costa-victor/wireless-robotic-arm-arduino/3D Files/Garra adaptada/EBA_01.00.013_R01_right_finger.STL

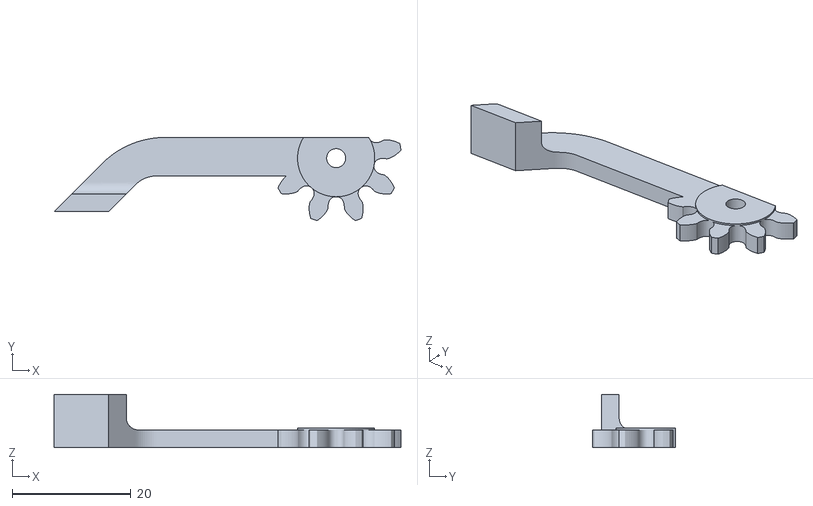
[picture p15: CAD file, 2020-02-10]
3D Files/Garra adaptada/EBA_01.00.013_R01_right_finger.STL
58.4 x 14.0 x 9.00
