costa-victor/wireless-robotic-arm-arduino/3D Files/stl/parte 9 - modificadaAutocad.stl

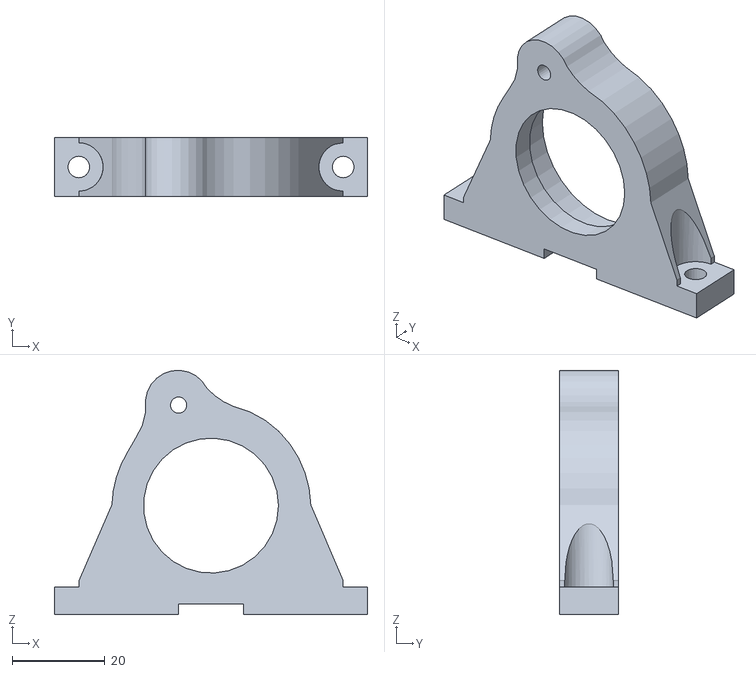
[picture p16: CAD file, 2020-02-10]
3D Files/stl/parte 9 - modificadaAutocad.stl
67.7 x 12.8 x 52.8
