costa-victor/wireless-robotic-arm-arduino/3D Files/Garra adaptada/EBA_01.00.004_forward_drive_arm.STL

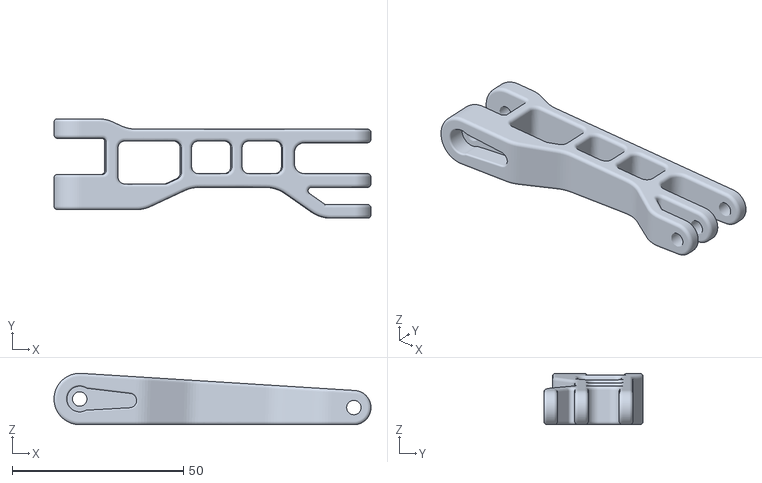
[picture p17: CAD file, 2020-02-10]
3D Files/Garra adaptada/EBA_01.00.004_forward_drive_arm.STL
92.5 x 29.0 x 15.0
