costa-victor/wireless-robotic-arm-arduino/3D Files/stl/parte 23 - autocad.stl

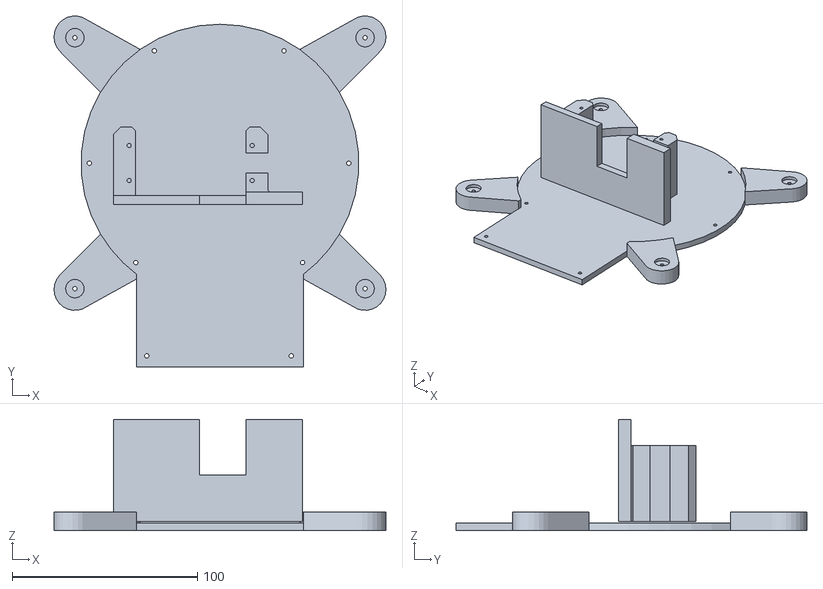
[picture p18: CAD file, 2020-02-10]
3D Files/stl/parte 23 - autocad.stl
179.2 x 189.3 x 60.0
