costa-victor/wireless-robotic-arm-arduino/3D Files/Garra adaptada/EBA_01.00.001.STL

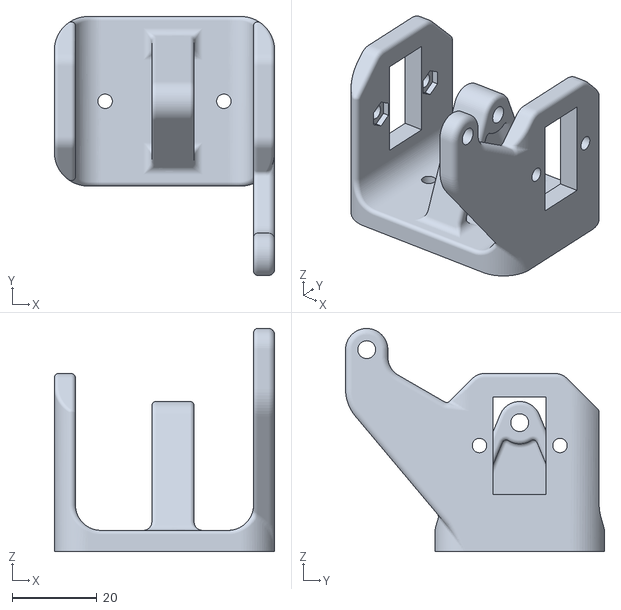
[picture p19: CAD file, 2020-02-10]
3D Files/Garra adaptada/EBA_01.00.001.STL
52.0 x 61.1 x 52.6
