costa-victor/wireless-robotic-arm-arduino/3D Files/stl/apoioAuxiliarDaPt4-2.stl

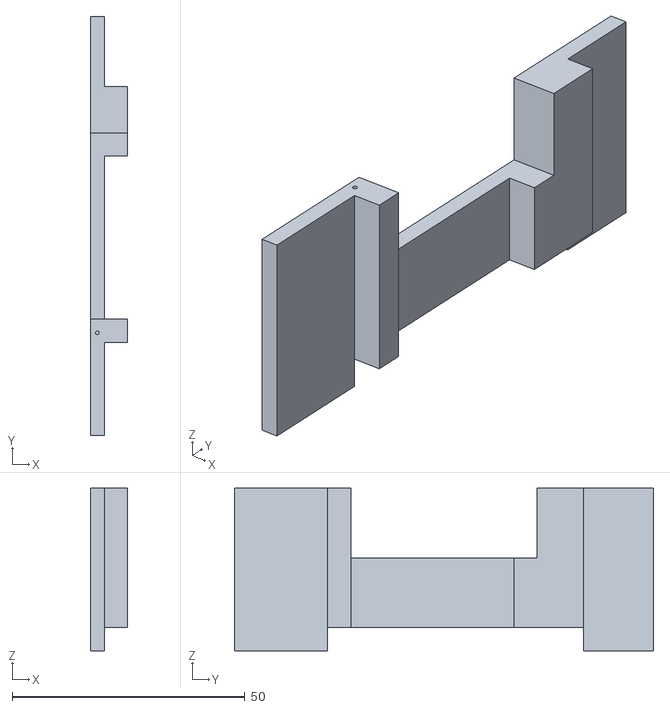
[picture p20: CAD file, 2020-02-10]
3D Files/stl/apoioAuxiliarDaPt4-2.stl
8.00 x 90.0 x 35.0
