costa-victor/wireless-robotic-arm-arduino/3D Files/Garra adaptada/EBA_01.00.009_servo_plate.STL

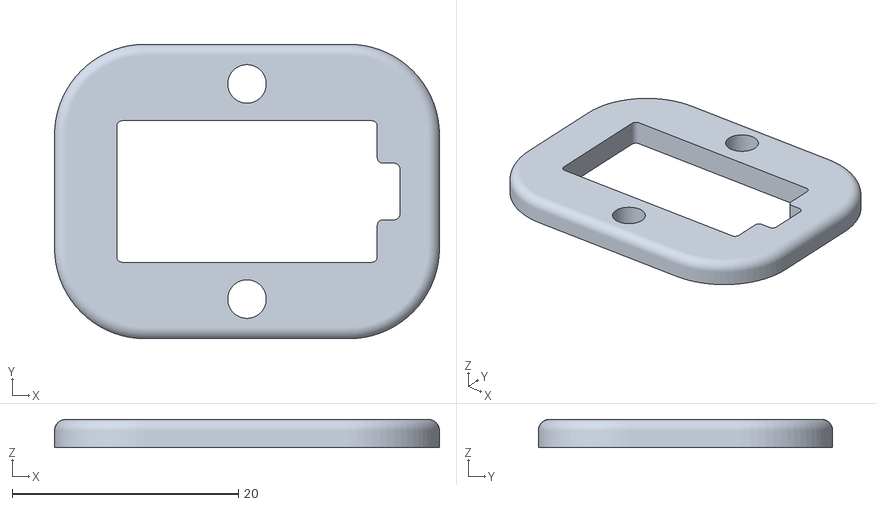
[picture p21: CAD file, 2020-02-10]
3D Files/Garra adaptada/EBA_01.00.009_servo_plate.STL
34.0 x 26.0 x 2.50
