costa-victor/wireless-robotic-arm-arduino/3D Files/stl/PART_8.stl

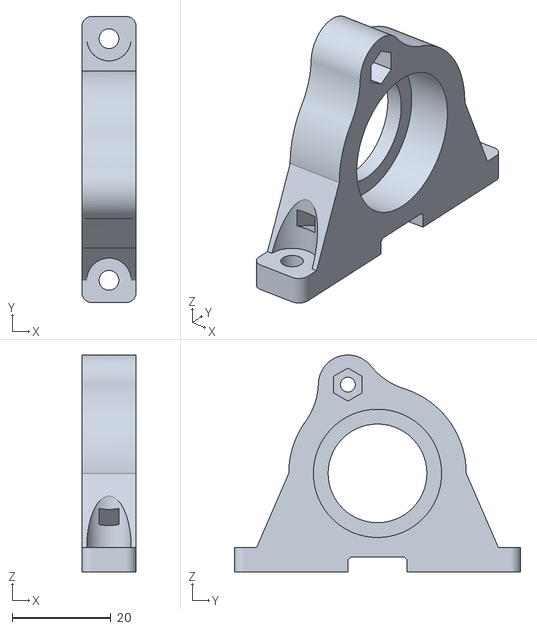
[picture p22: CAD file, 2020-02-10]
3D Files/stl/PART_8.stl
11.0 x 58.0 x 44.0
