costa-victor/wireless-robotic-arm-arduino/3D Files/Garra adaptada/EBA_01.00.015_drive_gear.STL

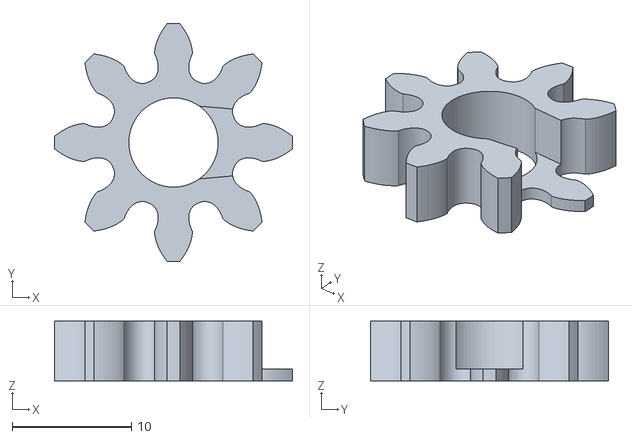
[picture p23: CAD file, 2020-02-10]
3D Files/Garra adaptada/EBA_01.00.015_drive_gear.STL
20.0 x 20.0 x 5.00
