costa-victor/wireless-robotic-arm-arduino/3D Files/stl/Peça 11 - sketchup.stl

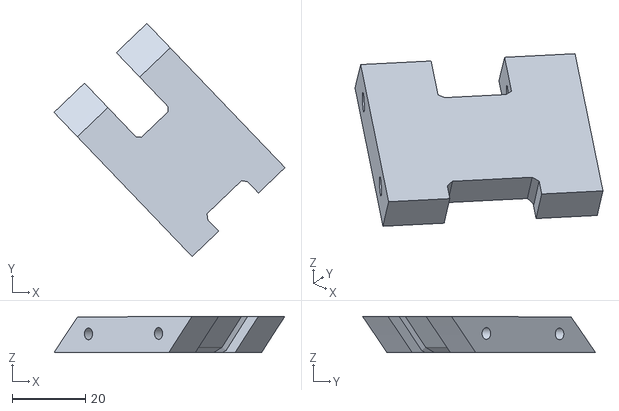
[picture p24: CAD file, 2020-02-10]
3D Files/stl/Peça 11 - sketchup.stl
62.9 x 63.5 x 9.90
