costa-victor/wireless-robotic-arm-arduino/3D Files/Garra adaptada/EBA_01.00.006_triangular_link.STL

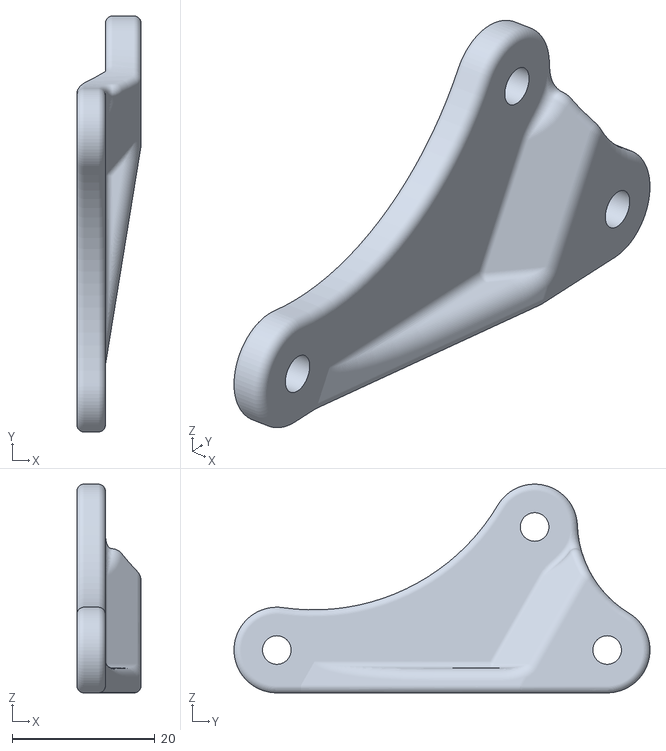
[picture p25: CAD file, 2020-02-10]
3D Files/Garra adaptada/EBA_01.00.006_triangular_link.STL
9.00 x 58.3 x 29.2
