costa-victor/wireless-robotic-arm-arduino/3D Files/stl/parte 12 - autocad.stl

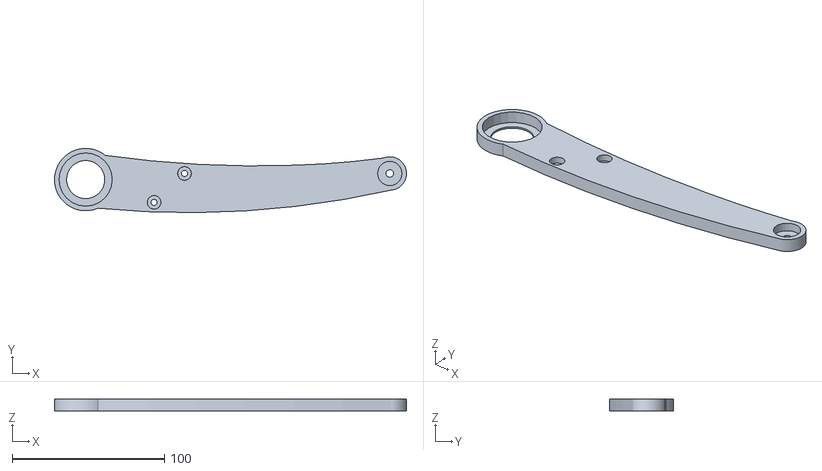
[picture p26: CAD file, 2020-02-10]
3D Files/stl/parte 12 - autocad.stl
231.5 x 42.2 x 8.00
