costa-victor/wireless-robotic-arm-arduino/3D Files/Garra adaptada/EBA_01.00.014_R01_left_finger.STL

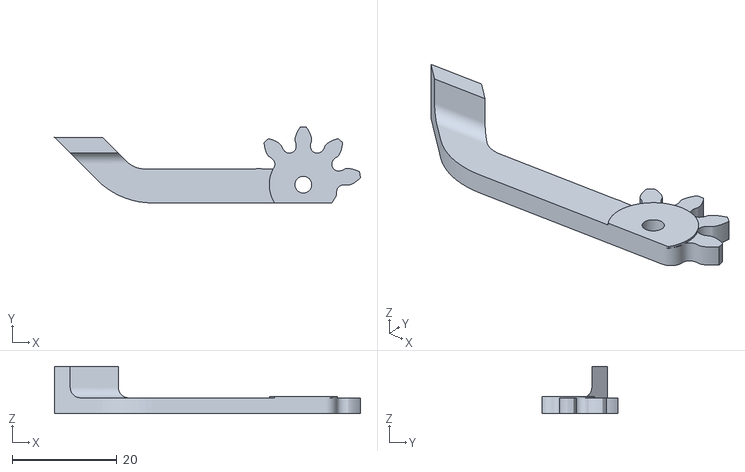
[picture p27: CAD file, 2020-02-10]
3D Files/Garra adaptada/EBA_01.00.014_R01_left_finger.STL
58.4 x 14.5 x 9.00
