costa-victor/wireless-robotic-arm-arduino/3D Files/stl/PART_13.stl

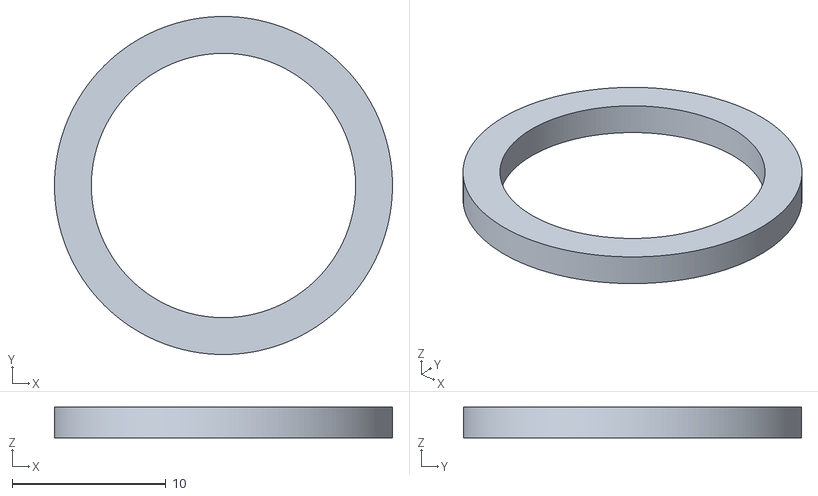
[picture p28: CAD file, 2020-02-10]
3D Files/stl/PART_13.stl
22.0 x 22.0 x 2.00
