costa-victor/wireless-robotic-arm-arduino/3D Files/Garra adaptada/EBA_01.00.011_round_plate.STL

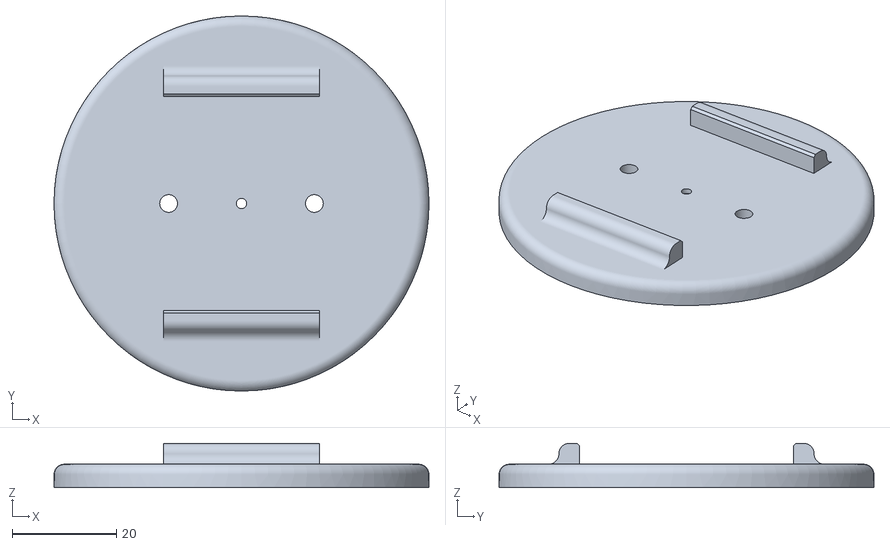
[picture p29: CAD file, 2020-02-10]
3D Files/Garra adaptada/EBA_01.00.011_round_plate.STL
72.0 x 72.0 x 8.50
