costa-victor/wireless-robotic-arm-arduino/3D Files/stl/parte 1 - autocad - pt1.stl

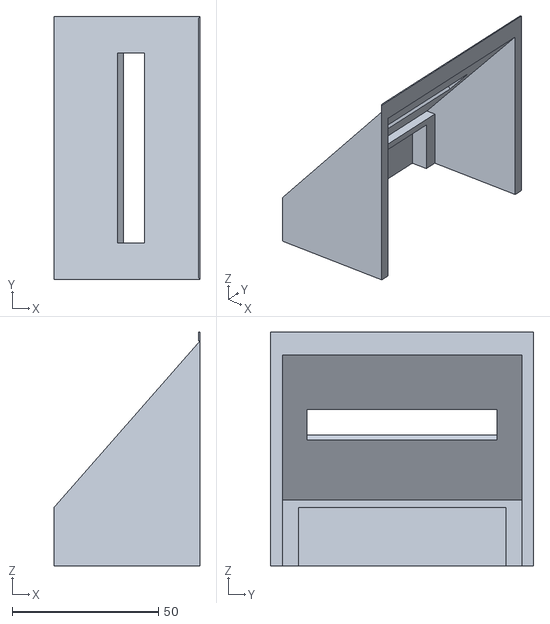
[picture p30: CAD file, 2020-02-10]
3D Files/stl/parte 1 - autocad - pt1.stl
50.0 x 90.1 x 80.0
