costa-victor/wireless-robotic-arm-arduino/3D Files/Garra adaptada/EBA_01.00.017_R01_ramp.STL

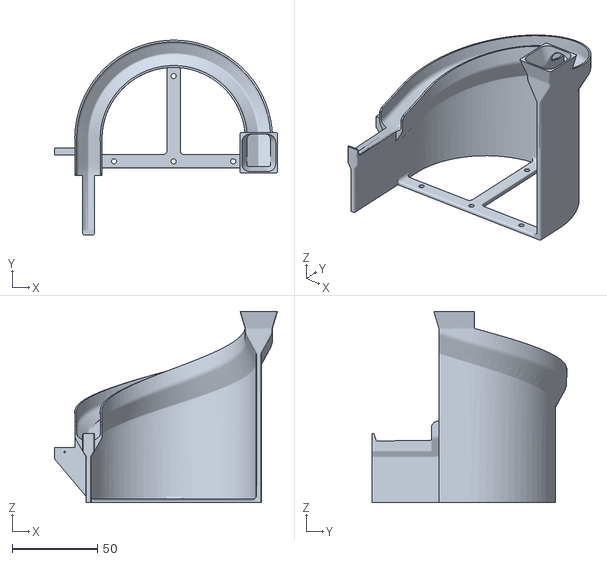
[picture p31: CAD file, 2020-02-10]
3D Files/Garra adaptada/EBA_01.00.017_R01_ramp.STL
131.0 x 114.4 x 112.3
