costa-victor/wireless-robotic-arm-arduino/3D Files/stl/Peça 16 - autocad - pt3.stl

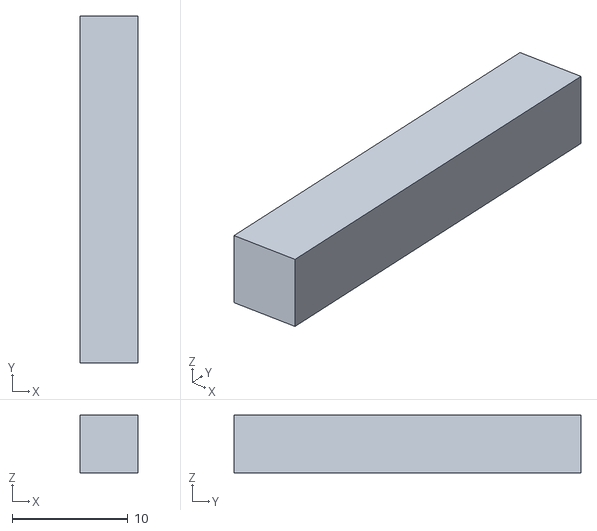
[picture p32: CAD file, 2020-02-10]
3D Files/stl/Peça 16 - autocad - pt3.stl
5.00 x 30.0 x 5.00
