costa-victor/wireless-robotic-arm-arduino/3D Files/Garra adaptada/EBA_01.00.012_R01_claw_support.STL

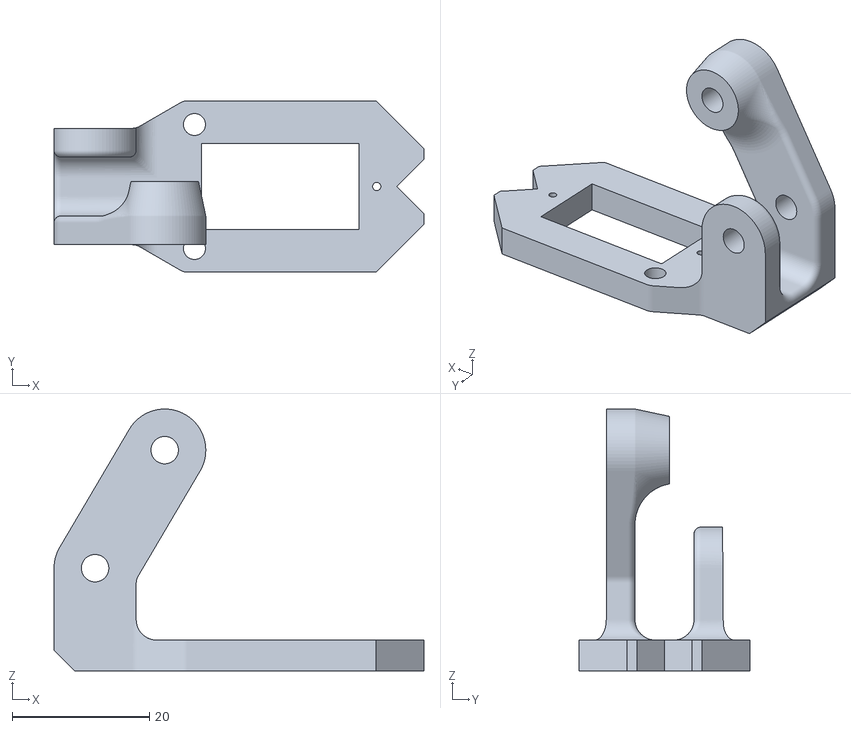
[picture p33: CAD file, 2020-02-10]
3D Files/Garra adaptada/EBA_01.00.012_R01_claw_support.STL
54.0 x 25.0 x 38.2
