costa-victor/wireless-robotic-arm-arduino/3D Files/stl/apoioAuxiliarDoMotor.stl

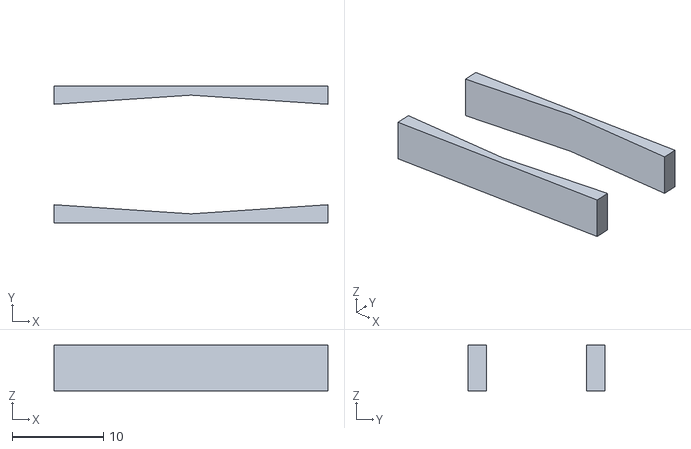
[picture p34: CAD file, 2020-02-10]
3D Files/stl/apoioAuxiliarDoMotor.stl
30.0 x 15.0 x 5.00
