costa-victor/wireless-robotic-arm-arduino/3D Files/stl/PART_6.stl

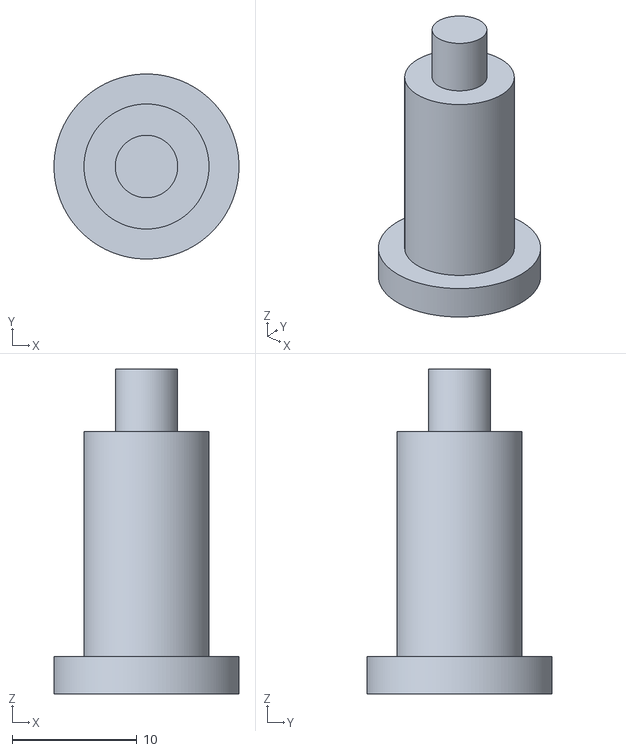
[picture p35: CAD file, 2020-02-10]
3D Files/stl/PART_6.stl
14.8 x 14.8 x 26.0
