costa-victor/wireless-robotic-arm-arduino/3D Files/stl/Peça 16 - autocad - pt1.stl

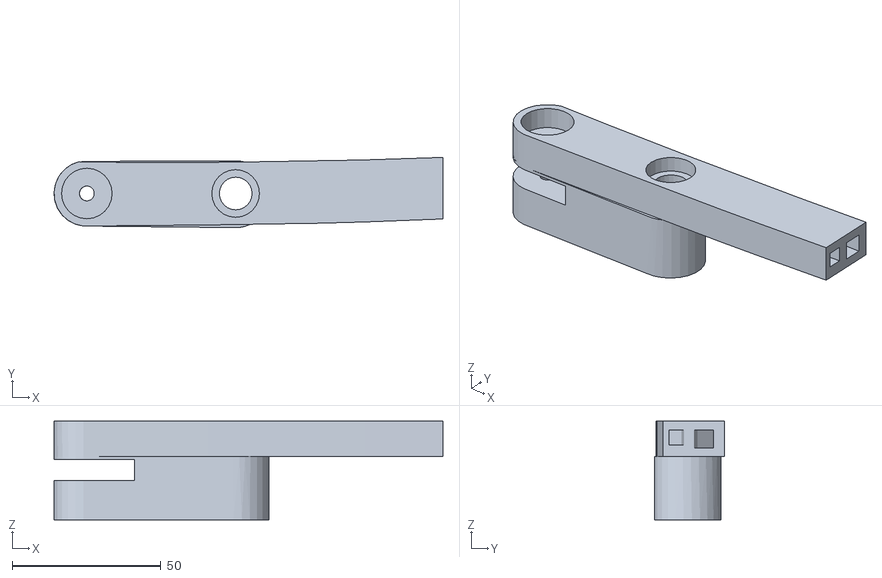
[picture p36: CAD file, 2020-02-10]
3D Files/stl/Peça 16 - autocad - pt1.stl
130.7 x 23.6 x 33.3
