costa-victor/wireless-robotic-arm-arduino/3D Files/stl/parte 2 - autocad.stl

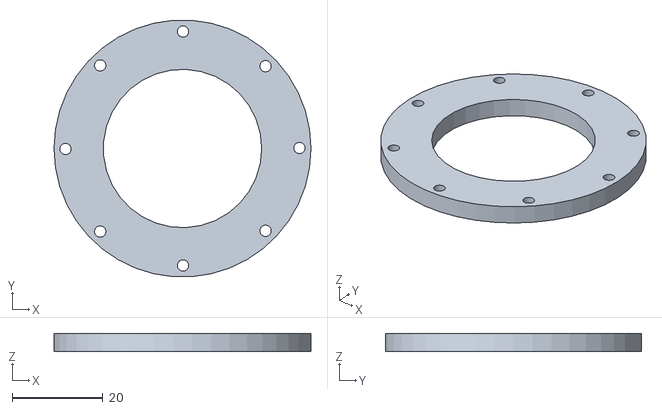
[picture p37: CAD file, 2020-02-10]
3D Files/stl/parte 2 - autocad.stl
56.6 x 56.4 x 4.00
