costa-victor/wireless-robotic-arm-arduino/3D Files/stl/apoioAuxiliarDaPt4.stl

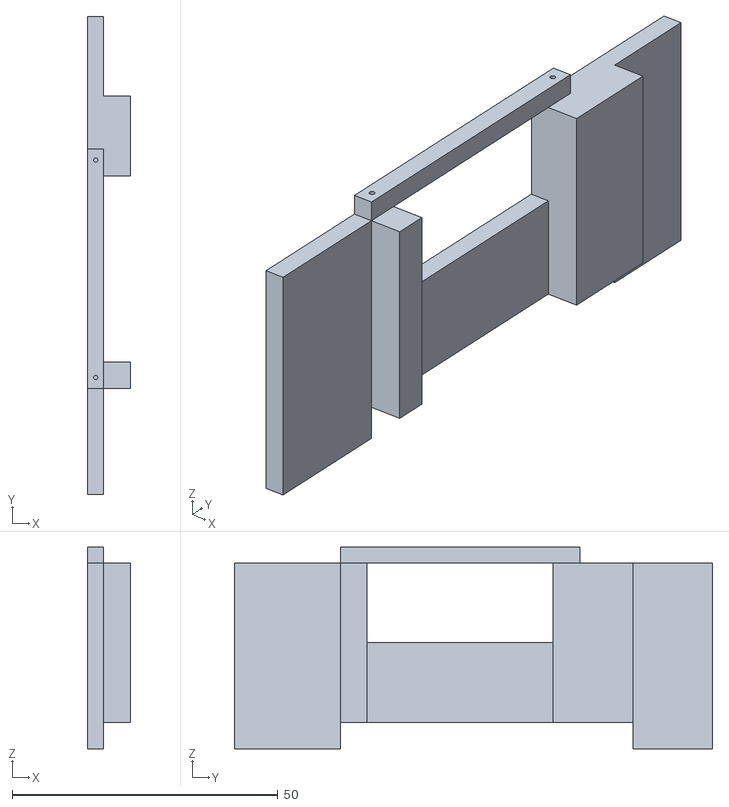
[picture p38: CAD file, 2020-02-10]
3D Files/stl/apoioAuxiliarDaPt4.stl
8.00 x 90.0 x 38.0
