costa-victor/wireless-robotic-arm-arduino/3D Files/stl/PART_5.stl

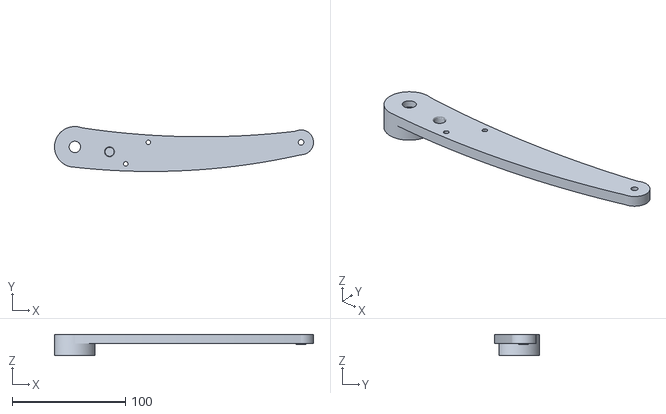
[picture p39: CAD file, 2020-02-10]
3D Files/stl/PART_5.stl
229.0 x 39.7 x 19.0
