costa-victor/wireless-robotic-arm-arduino/3D Files/stl/4x_PART_24.stl

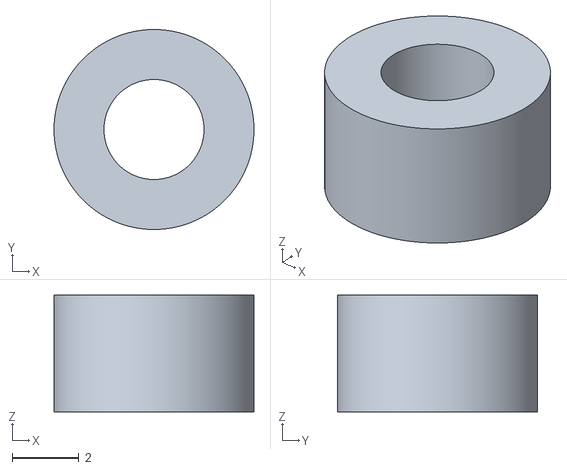
[picture p40: CAD file, 2020-02-10]
3D Files/stl/4x_PART_24.stl
6.00 x 6.00 x 3.50
