costa-victor/wireless-robotic-arm-arduino/3D Files/stl/placa.stl

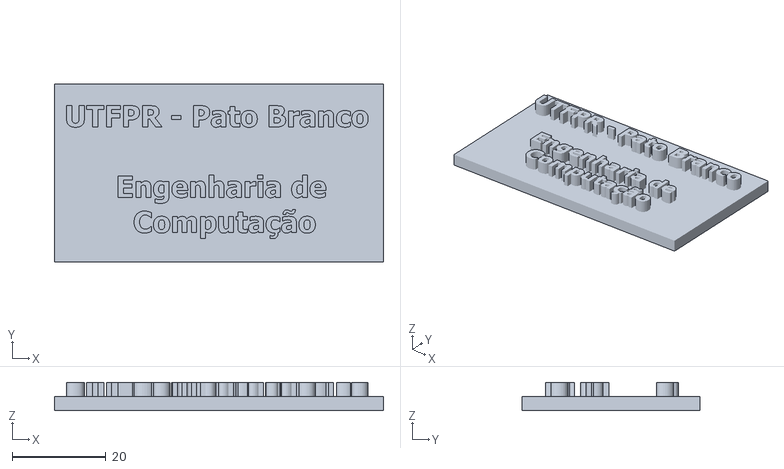
[picture p41: CAD file, 2020-02-10]
3D Files/stl/placa.stl
70.0 x 38.0 x 6.02
