costa-victor/wireless-robotic-arm-arduino/3D Files/stl/PART_18.stl

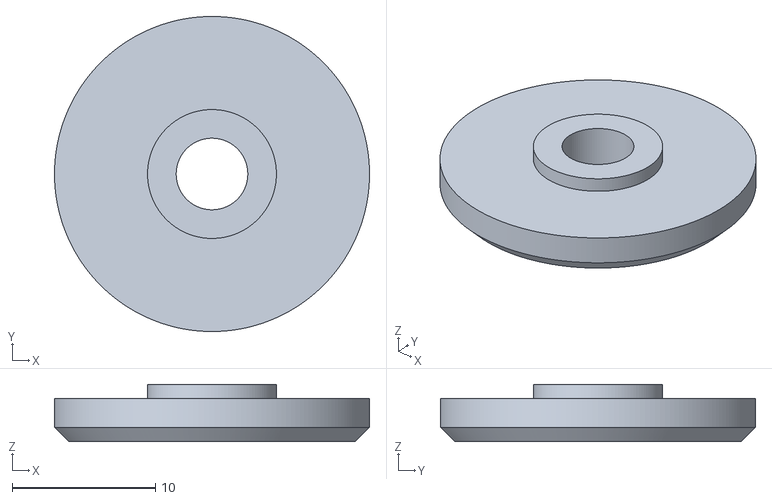
[picture p42: CAD file, 2020-02-10]
3D Files/stl/PART_18.stl
22.0 x 22.0 x 4.00
