costa-victor/wireless-robotic-arm-arduino/3D Files/stl/parte 23 - sketchup.1.stl

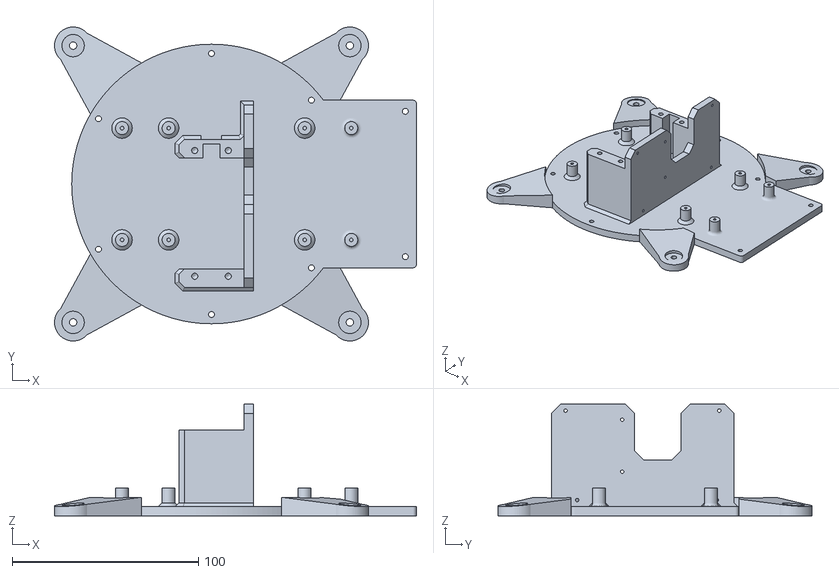
[picture p43: CAD file, 2020-02-10]
3D Files/stl/parte 23 - sketchup.1.stl
194.2 x 168.5 x 60.0
