costa-victor/wireless-robotic-arm-arduino/3D Files/stl/PART_21.stl

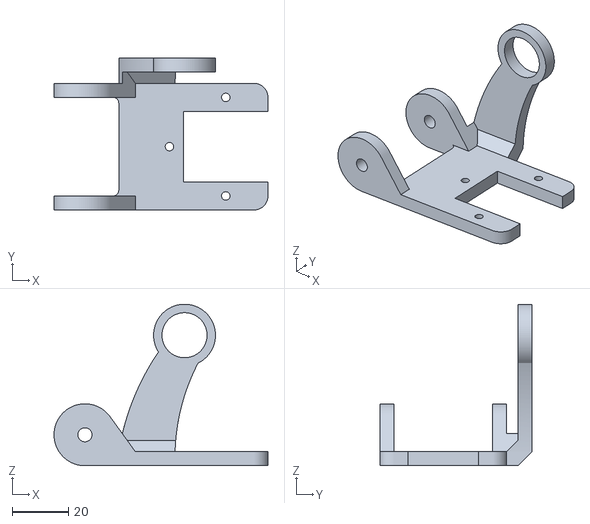
[picture p44: CAD file, 2020-02-10]
3D Files/stl/PART_21.stl
76.0 x 54.0 x 57.4
