costa-victor/wireless-robotic-arm-arduino/3D Files/stl/PART_14.stl

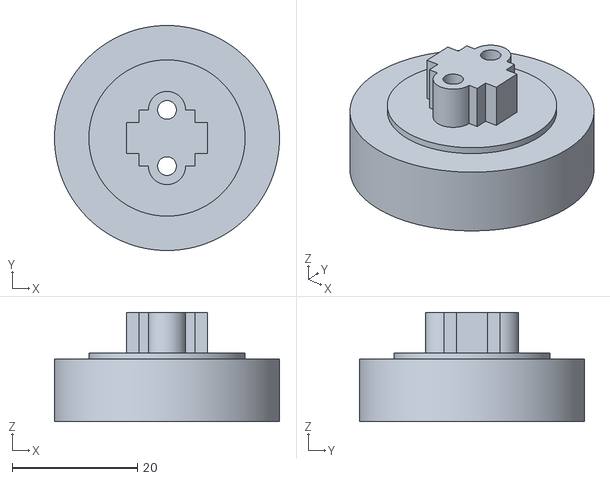
[picture p45: CAD file, 2020-02-10]
3D Files/stl/PART_14.stl
36.0 x 36.0 x 17.5
