costa-victor/wireless-robotic-arm-arduino/3D Files/stl/PART_1 - modificado.stl

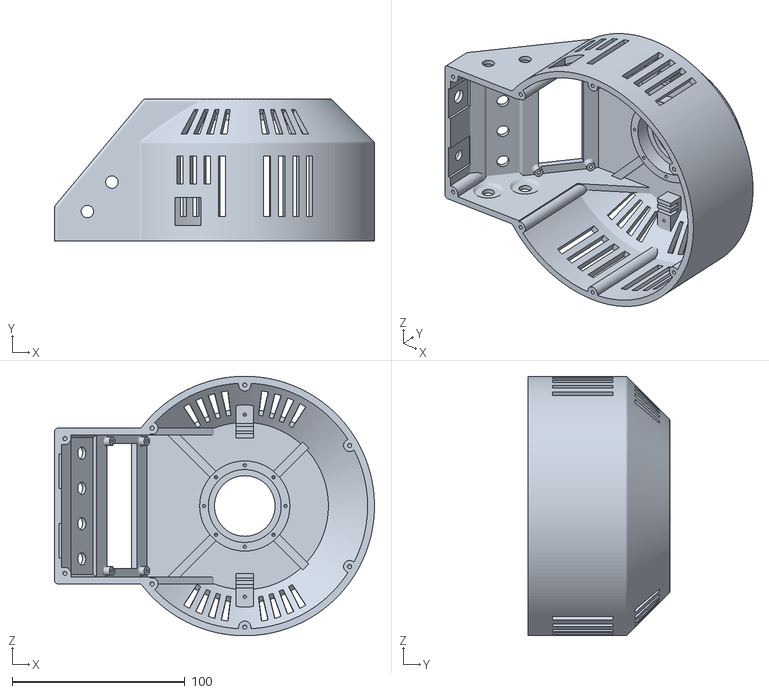
[picture p46: CAD file, 2020-02-10]
3D Files/stl/PART_1 - modificado.stl
185.0 x 82.0 x 150.0
