costa-victor/wireless-robotic-arm-arduino/3D Files/stl/Peça 16 - autocad - pt2.stl

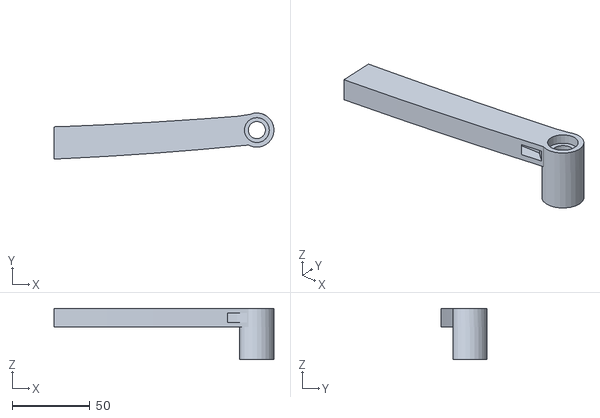
[picture p47: CAD file, 2020-02-10]
3D Files/stl/Peça 16 - autocad - pt2.stl
141.1 x 29.6 x 33.0
