costa-victor/wireless-robotic-arm-arduino/3D Files/stl/PART_12.stl

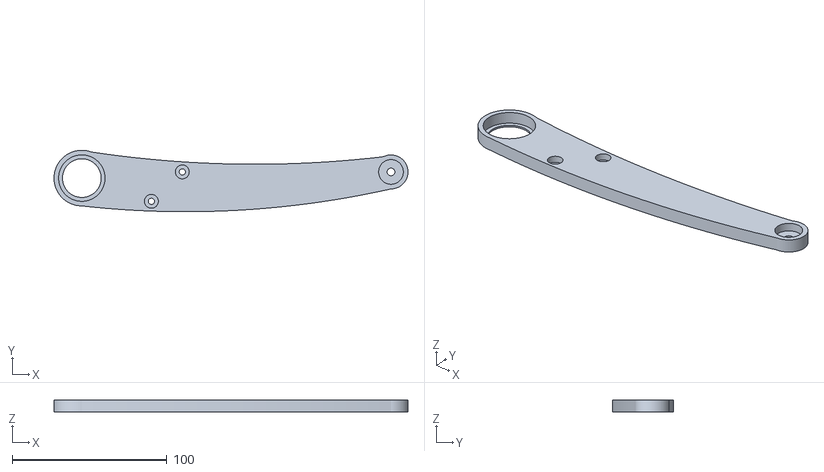
[picture p48: CAD file, 2020-02-10]
3D Files/stl/PART_12.stl
229.0 x 39.7 x 8.00
