costa-victor/wireless-robotic-arm-arduino/3D Files/stl/parte 1 - autocad - pt2.stl

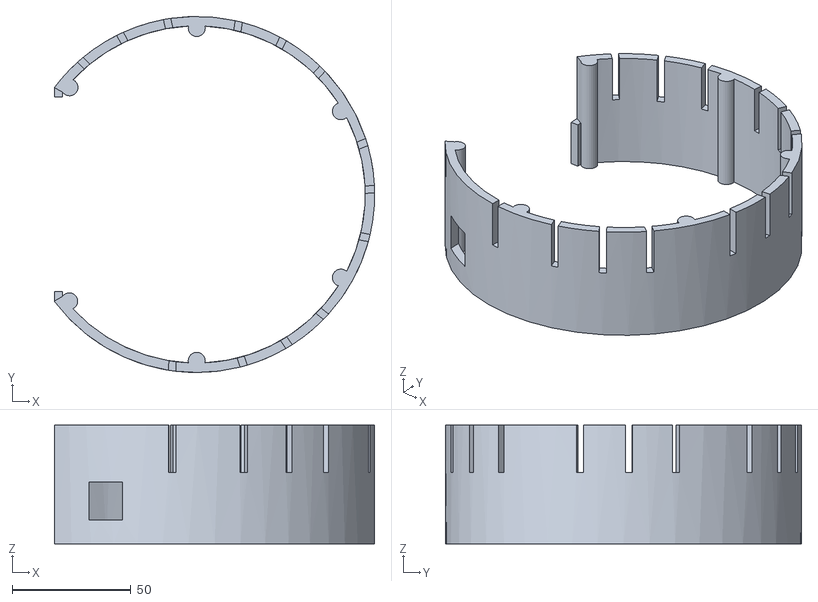
[picture p49: CAD file, 2020-02-10]
3D Files/stl/parte 1 - autocad - pt2.stl
135.0 x 150.0 x 50.0
