costa-victor/wireless-robotic-arm-arduino/3D Files/stl/PART_4.stl

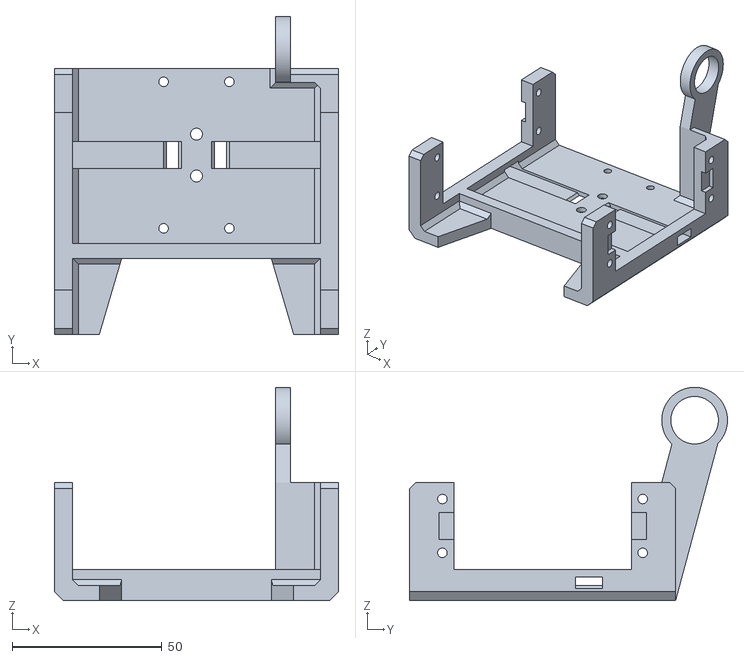
[picture p50: CAD file, 2020-02-10]
3D Files/stl/PART_4.stl
95.0 x 106.3 x 71.4
