costa-victor/wireless-robotic-arm-arduino/3D Files/stl/PART_16.stl

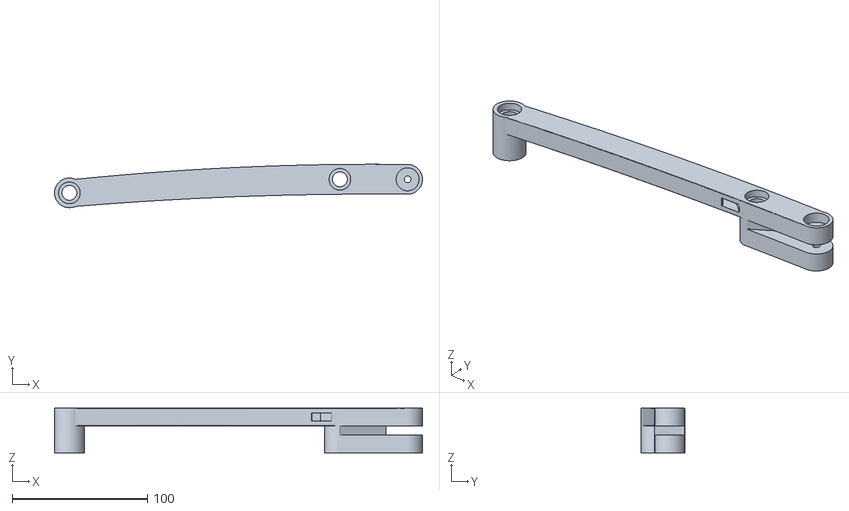
[picture p51: CAD file, 2020-02-10]
3D Files/stl/PART_16.stl
271.7 x 32.1 x 33.0
