costa-victor/wireless-robotic-arm-arduino/3D Files/stl/16x_PART_19.stl

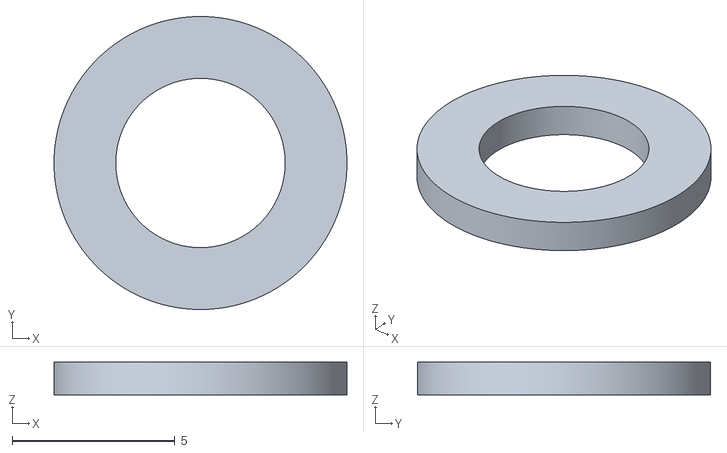
[picture p52: CAD file, 2020-02-10]
3D Files/stl/16x_PART_19.stl
9.00 x 9.00 x 1.00
