costa-victor/wireless-robotic-arm-arduino/3D Files/stl/PART_15.stl

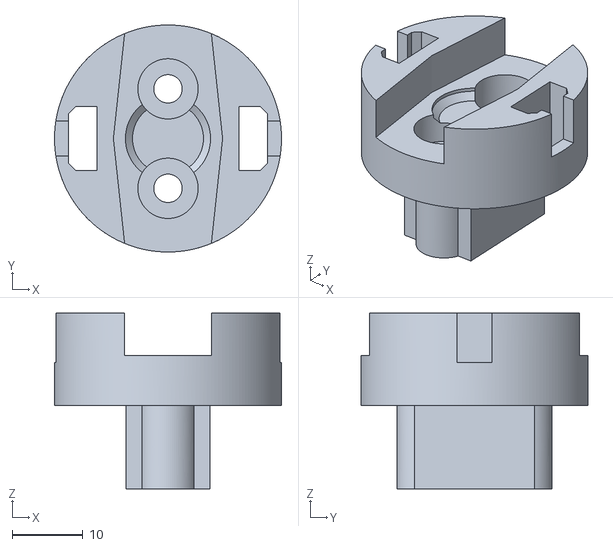
[picture p53: CAD file, 2020-02-10]
3D Files/stl/PART_15.stl
32.0 x 32.0 x 24.8
