costa-victor/wireless-robotic-arm-arduino/3D Files/stl/PART_11.stl

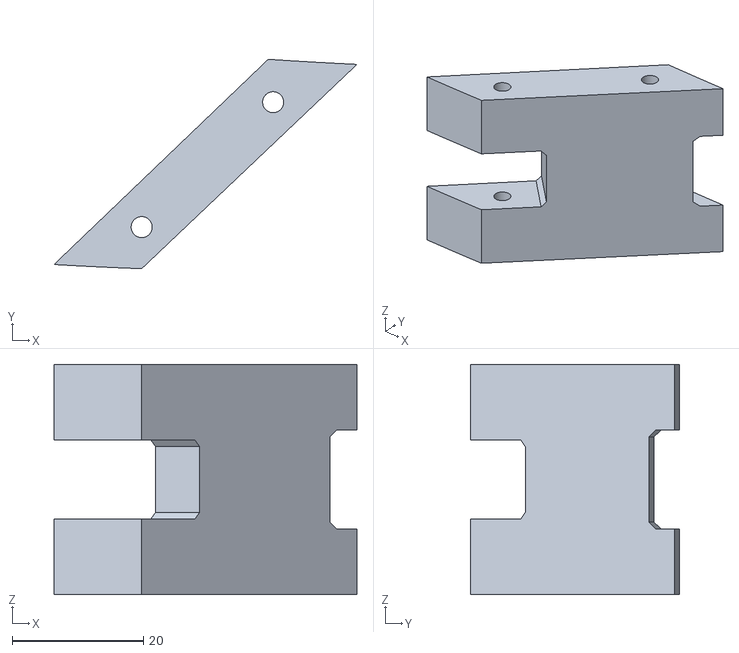
[picture p54: CAD file, 2020-02-10]
3D Files/stl/PART_11.stl
46.1 x 31.9 x 35.0
