costa-victor/wireless-robotic-arm-arduino/3D Files/stl/PART_2.stl

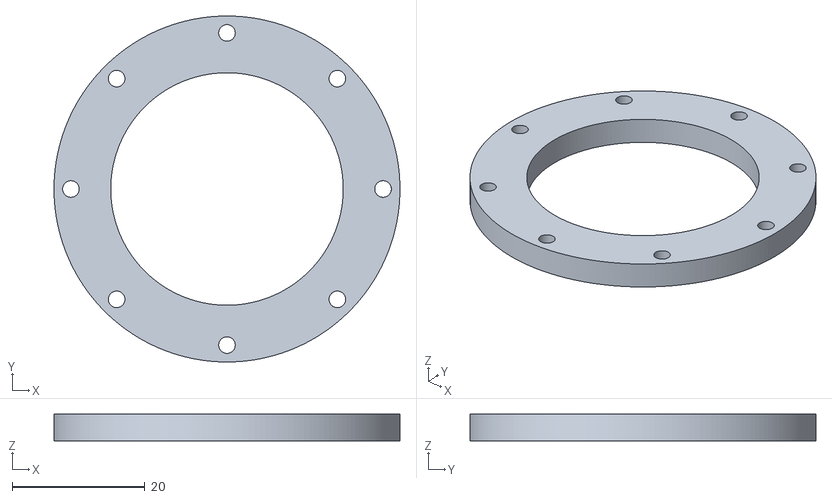
[picture p55: CAD file, 2020-02-10]
3D Files/stl/PART_2.stl
52.1 x 52.1 x 4.00
