costa-victor/wireless-robotic-arm-arduino/3D Files/stl/PART_7.stl

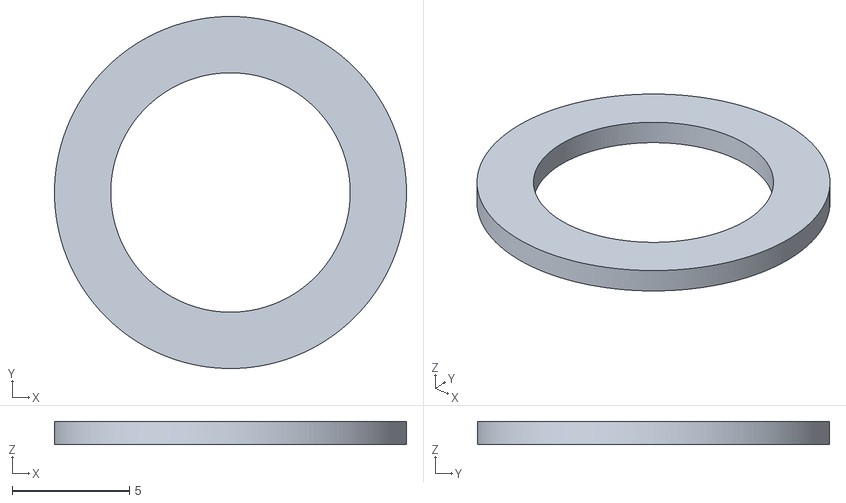
[picture p56: CAD file, 2020-02-10]
3D Files/stl/PART_7.stl
15.0 x 15.0 x 1.00
