costa-victor/wireless-robotic-arm-arduino/3D Files/stl/parte 1 - autocad - pt3.stl

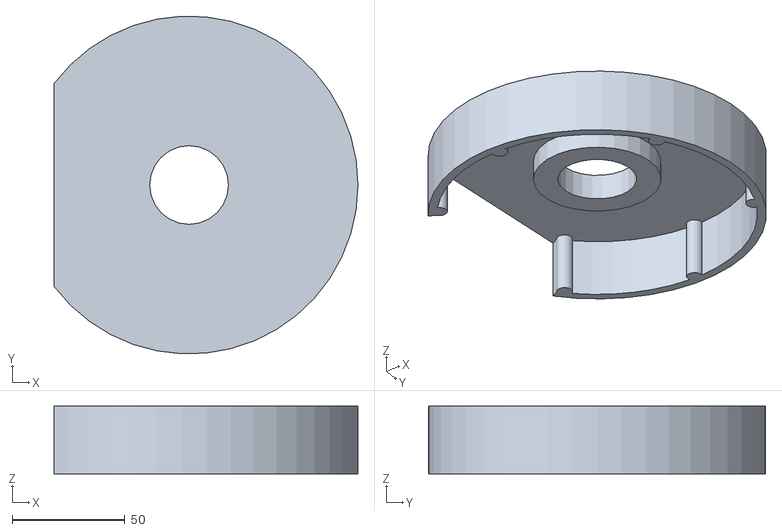
[picture p57: CAD file, 2020-02-10]
3D Files/stl/parte 1 - autocad - pt3.stl
135.0 x 149.8 x 30.0
