costa-victor/wireless-robotic-arm-arduino/3D Files/stl/PART_3.stl

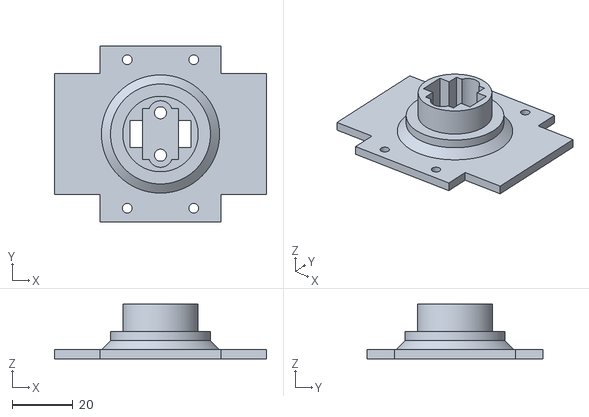
[picture p58: CAD file, 2020-02-10]
3D Files/stl/PART_3.stl
70.0 x 58.0 x 18.0
