costa-victor/wireless-robotic-arm-arduino/3D Files/stl/PART_23.stl

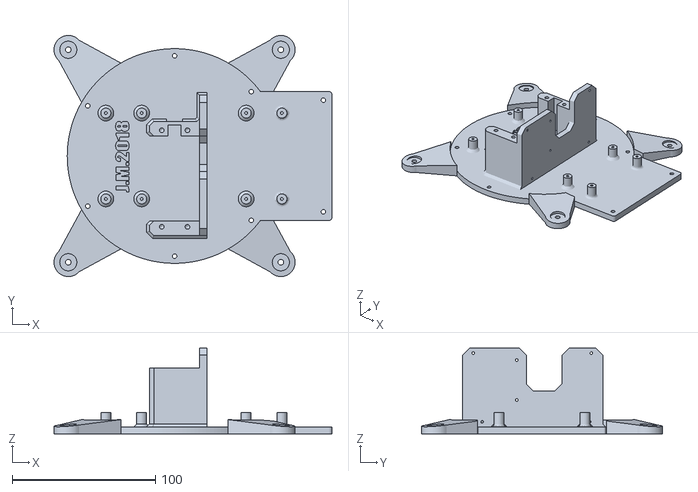
[picture p59: CAD file, 2020-02-10]
3D Files/stl/PART_23.stl
194.2 x 168.5 x 60.0
