costa-victor/wireless-robotic-arm-arduino/3D Files/stl/PART_20.stl

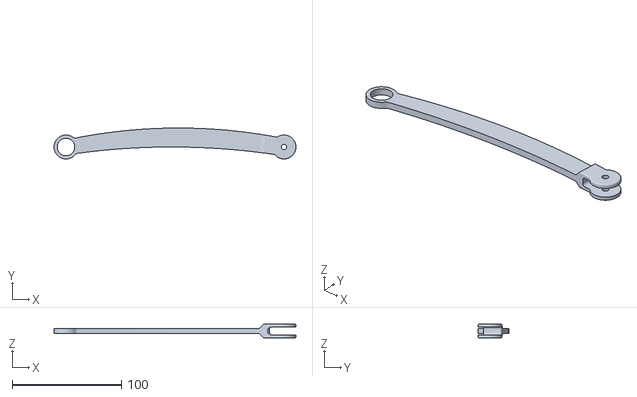
[picture p60: CAD file, 2020-02-10]
3D Files/stl/PART_20.stl
222.0 x 28.4 x 13.0
